migit/verhoBot/VerhoBot/hardware/CAD/images/VerhoBot_-_back.png

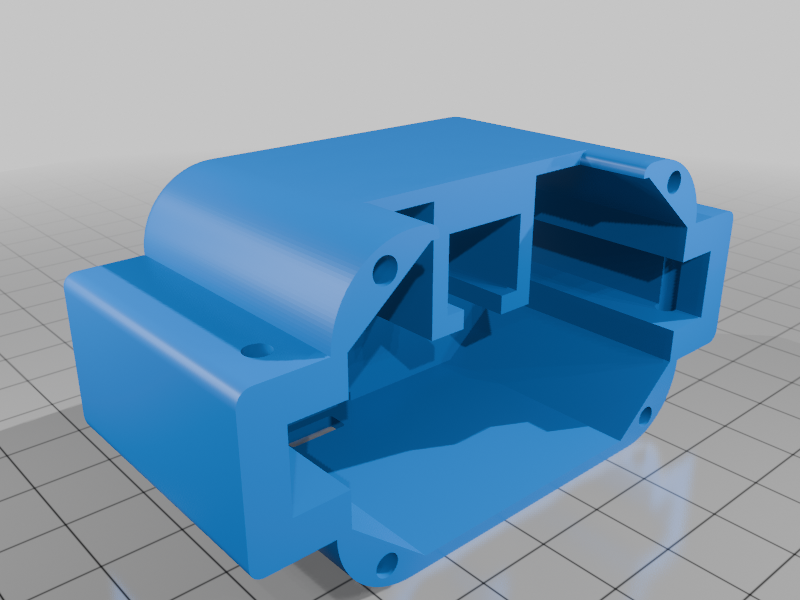
VerhoBot/hardware/CAD/images/VerhoBot_-_back.png
