migit/verhoBot/VerhoBot/hardware/VerhoBot_3D_PCB1.0.png

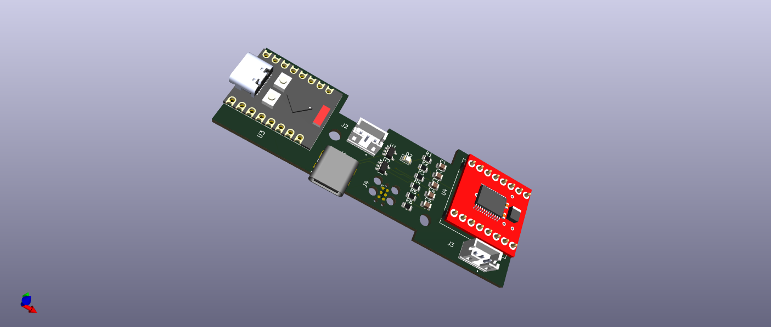
VerhoBot/hardware/VerhoBot_3D_PCB1.0.png
