migit/verhoBot/VerhoBot/hardware/verhoBot_charging.png

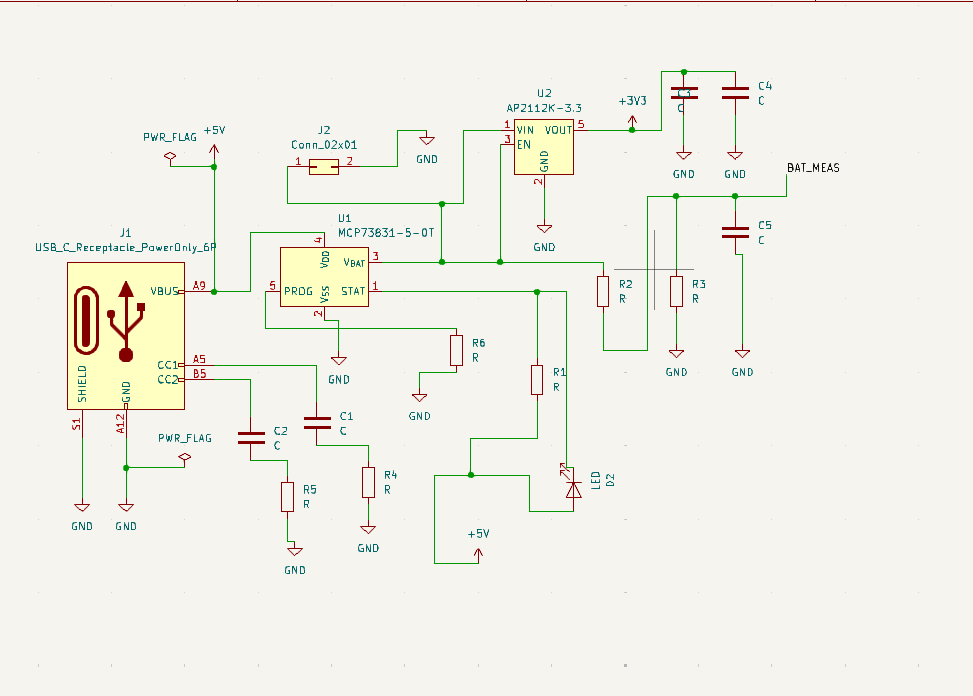
VerhoBot/hardware/verhoBot_charging.png
