migit/verhoBot/VerhoBot/hardware/verhoBotV1_schematic.png

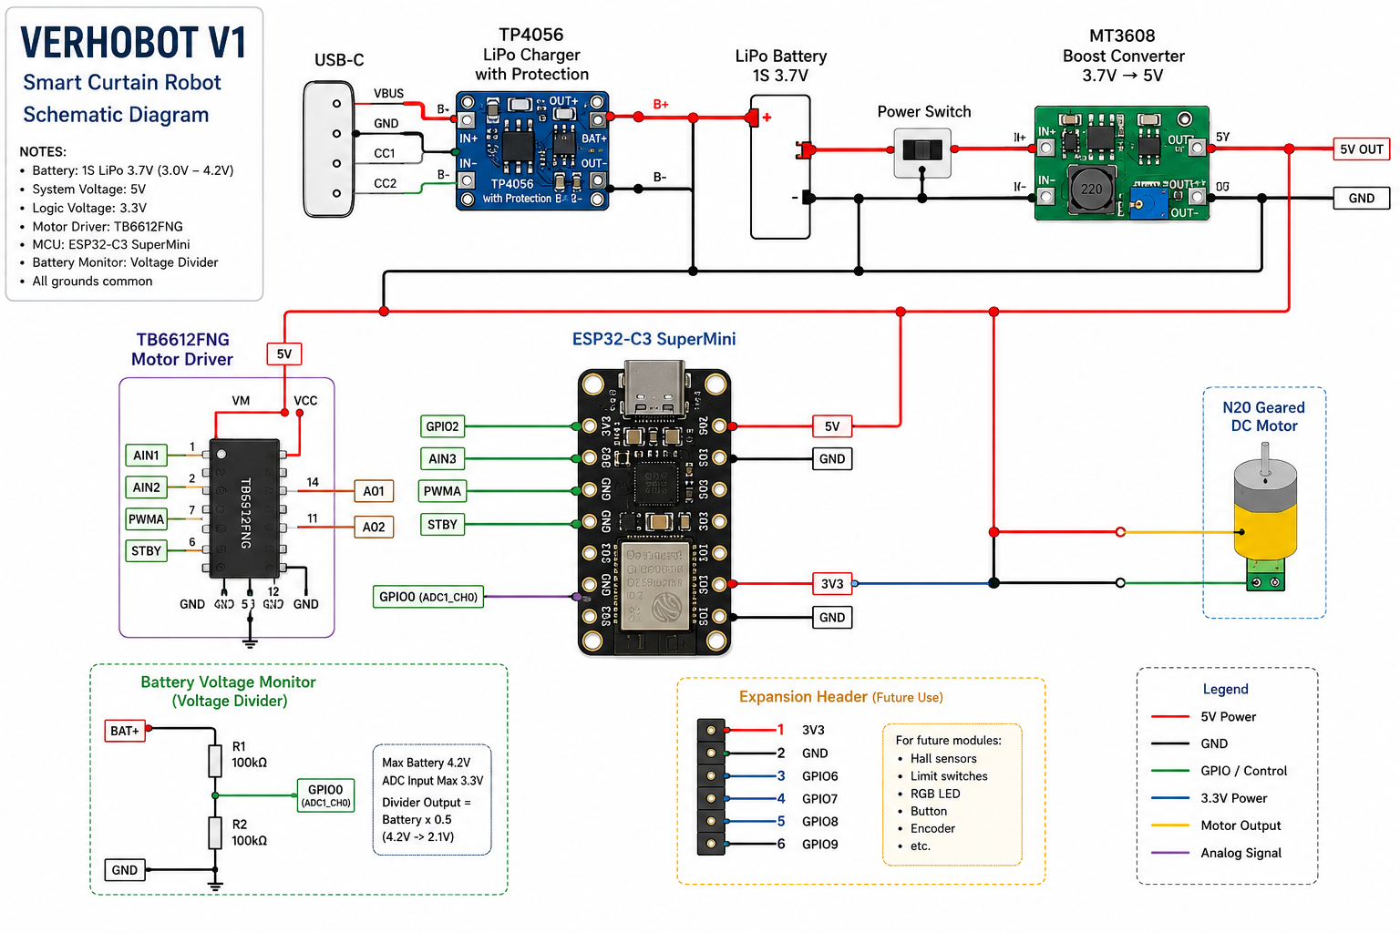
VerhoBot/hardware/verhoBotV1_schematic.png
